patglabs/NOMAD/pcb/mainboard/USB2.0&USB3.0.kicad_sch

## KiCad design pcb/mainboard/USB2.0&USB3.0.kicad_sch (2025-08-11)

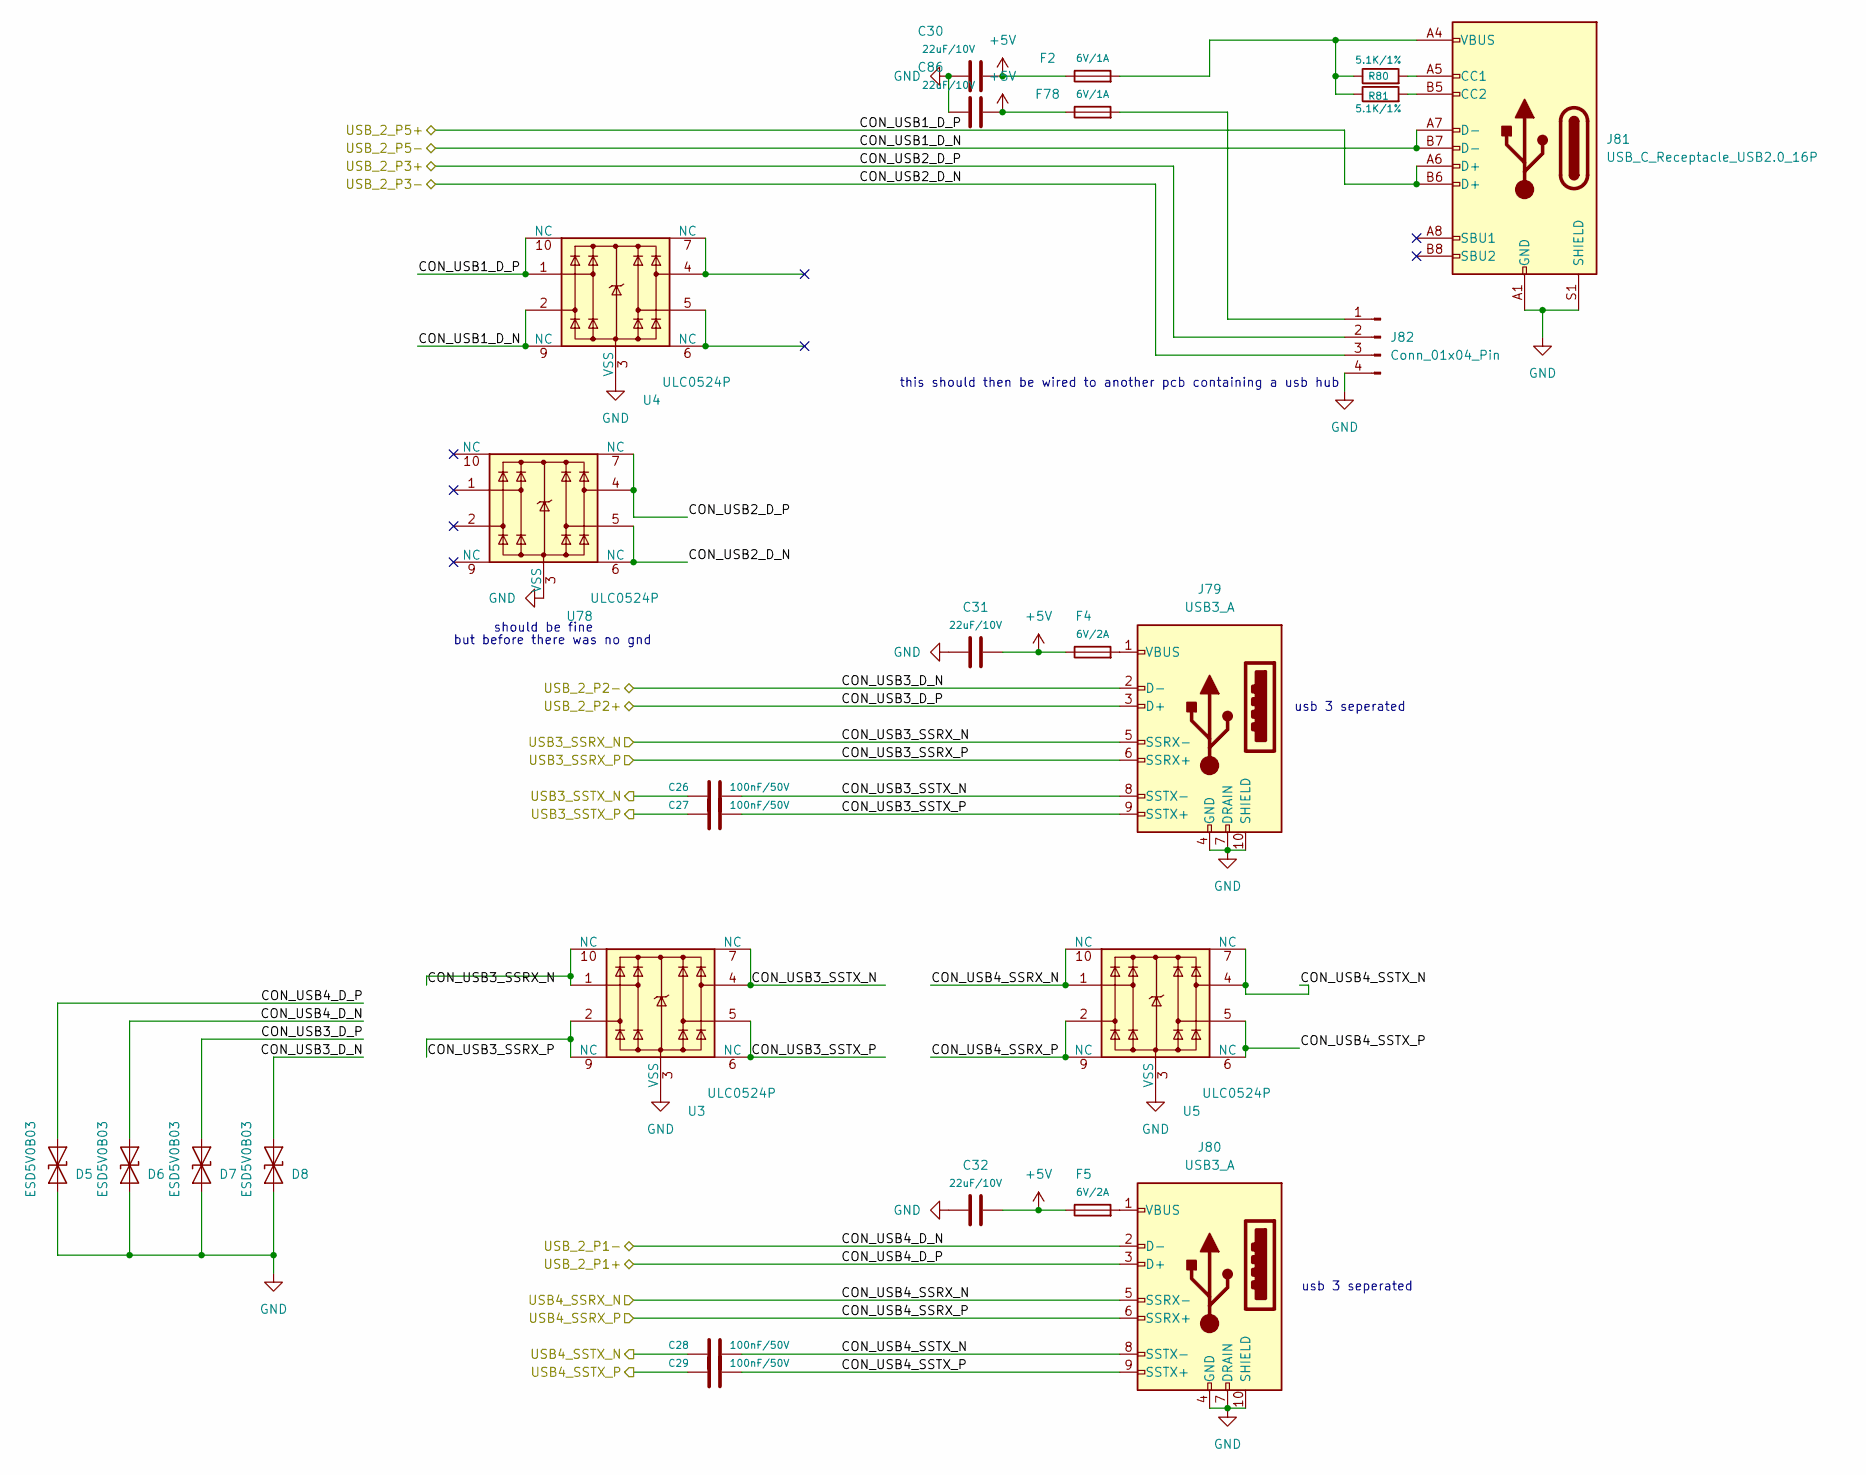
[picture p18: schematic USB2.0&USB3.0.kicad_sch]

Parts:
C26, C27, C28, C29: 100nF/50V; C_0402_1005Metric
C30, C31, C32, C86: 22uF/10V; C_0603_1608Metric
D5, D6, D7, D8: ESD5V0B03; D_0402_1005Metric
F2, F78: 6V/1A; Fuse_0805_2012Metric
F4: 6V/2A; R_0805_2012Metric
F5: 6V/2A; Fuse_0805_2012Metric
J79, J80: USB3_A; USB3_A_Molex_48393-001
J81: USB_C_Receptacle_USB2.0_16P; USB_C_Receptacle_GCT_USB4085
J82: Conn_01x04_Pin; PinHeader_1x04_P2.54mm_Vertical
R80, R81: 5.1K/1%; R_0402_1005Metric
U3, U4, U5, U78: ULC0524P; Diodes_UDFN-10_1.0x2.5mm_P0.5mm

Connections:
+5V: C30.2, C31.2, C32.2, C86.2, F2.1, F4.1, F5.1, F78.1
CON_USB1_D_N: J81.A7 (D-), J81.B7 (D-), U4.2, U4.9 (NC)
CON_USB1_D_P: J81.A6 (D+), J81.B6 (D+), U4.1, U4.10 (NC)
CON_USB2_D_N: J82.3, U78.5, U78.6 (NC)
CON_USB2_D_P: J82.2, U78.4, U78.7 (NC)
CON_USB3_D_N: D8.2 (A2), J79.2 (D-)
CON_USB3_D_P: D7.2 (A2), J79.3 (D+)
CON_USB3_SSRX_N: J79.5 (SSRX-), U3.1, U3.10 (NC)
CON_USB3_SSRX_P: J79.6 (SSRX+), U3.2, U3.9 (NC)
CON_USB3_SSTX_N: C26.2, J79.8 (SSTX-), U3.4, U3.7 (NC)
CON_USB3_SSTX_P: C27.2, J79.9 (SSTX+), U3.5, U3.6 (NC)
CON_USB4_D_N: D6.2 (A2), J80.2 (D-)
CON_USB4_D_P: D5.2 (A2), J80.3 (D+)
CON_USB4_SSRX_N: J80.5 (SSRX-), U5.1, U5.10 (NC)
CON_USB4_SSRX_P: J80.6 (SSRX+), U5.2, U5.9 (NC)
CON_USB4_SSTX_N: C28.2, J80.8 (SSTX-), U5.4, U5.7 (NC)
CON_USB4_SSTX_P: C29.2, J80.9 (SSTX+), U5.5, U5.6 (NC)
GND: C30.1, C31.1, C32.1, C86.1, D5.1 (A1), D6.1 (A1), D7.1 (A1), D8.1 (A1), J79.4 (GND), J79.7 (DRAIN), J79.10 (SHIELD), J80.4 (GND), J80.7 (DRAIN), J80.10 (SHIELD), J81.A1 (GND), J81.A12 (GND), J81.B1 (GND), J81.B12 (GND), J81.S1 (SHIELD), J82.4, U3.3 (VSS), U3.8 (VSS), U4.3 (VSS), U4.8 (VSS), U5.3 (VSS), U5.8 (VSS), U78.3 (VSS), U78.8 (VSS)
unnamed: F2.2, J81.A4 (VBUS), J81.A9 (VBUS), J81.B4 (VBUS), J81.B9 (VBUS), R80.1, R81.1
unnamed: F4.2, J79.1 (VBUS)
unnamed: F5.2, J80.1 (VBUS)
unnamed: F78.2, J82.1
unnamed: J81.A5 (CC1), R80.2
unnamed: J81.B5 (CC2), R81.2
unnamed: U4.4, U4.7 (NC)
unnamed: U4.5, U4.6 (NC)
USB3_SSTX_N: C26.1
USB3_SSTX_P: C27.1
USB4_SSTX_N: C28.1
USB4_SSTX_P: C29.1

Notes on the sheet:
but before there was no gnd
usb 3 seperated
this should then be wired to another pcb containing a usb hub
should be fine
